Tirthak-bot/Mech-Keeb/PCB/PCB Images/PCB Back.png

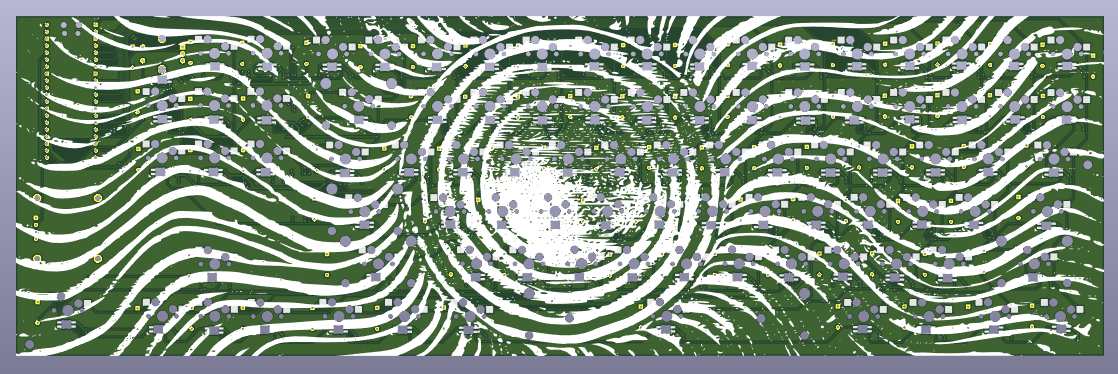
PCB/PCB Images/PCB Back.png
