Tirthak-bot/Mech-Keeb/PCB/PCB Images/PCB Front With Components.png

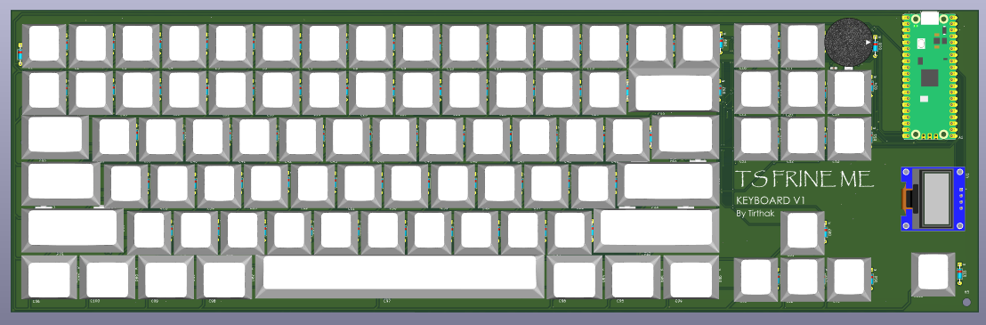
PCB/PCB Images/PCB Front With Components.png
