Tirthak-bot/Mech-Keeb/PCB/Mechanical LP Keyboard.kicad_sch

## KiCad design PCB/Mechanical LP Keyboard.kicad_sch (2026-06-20)

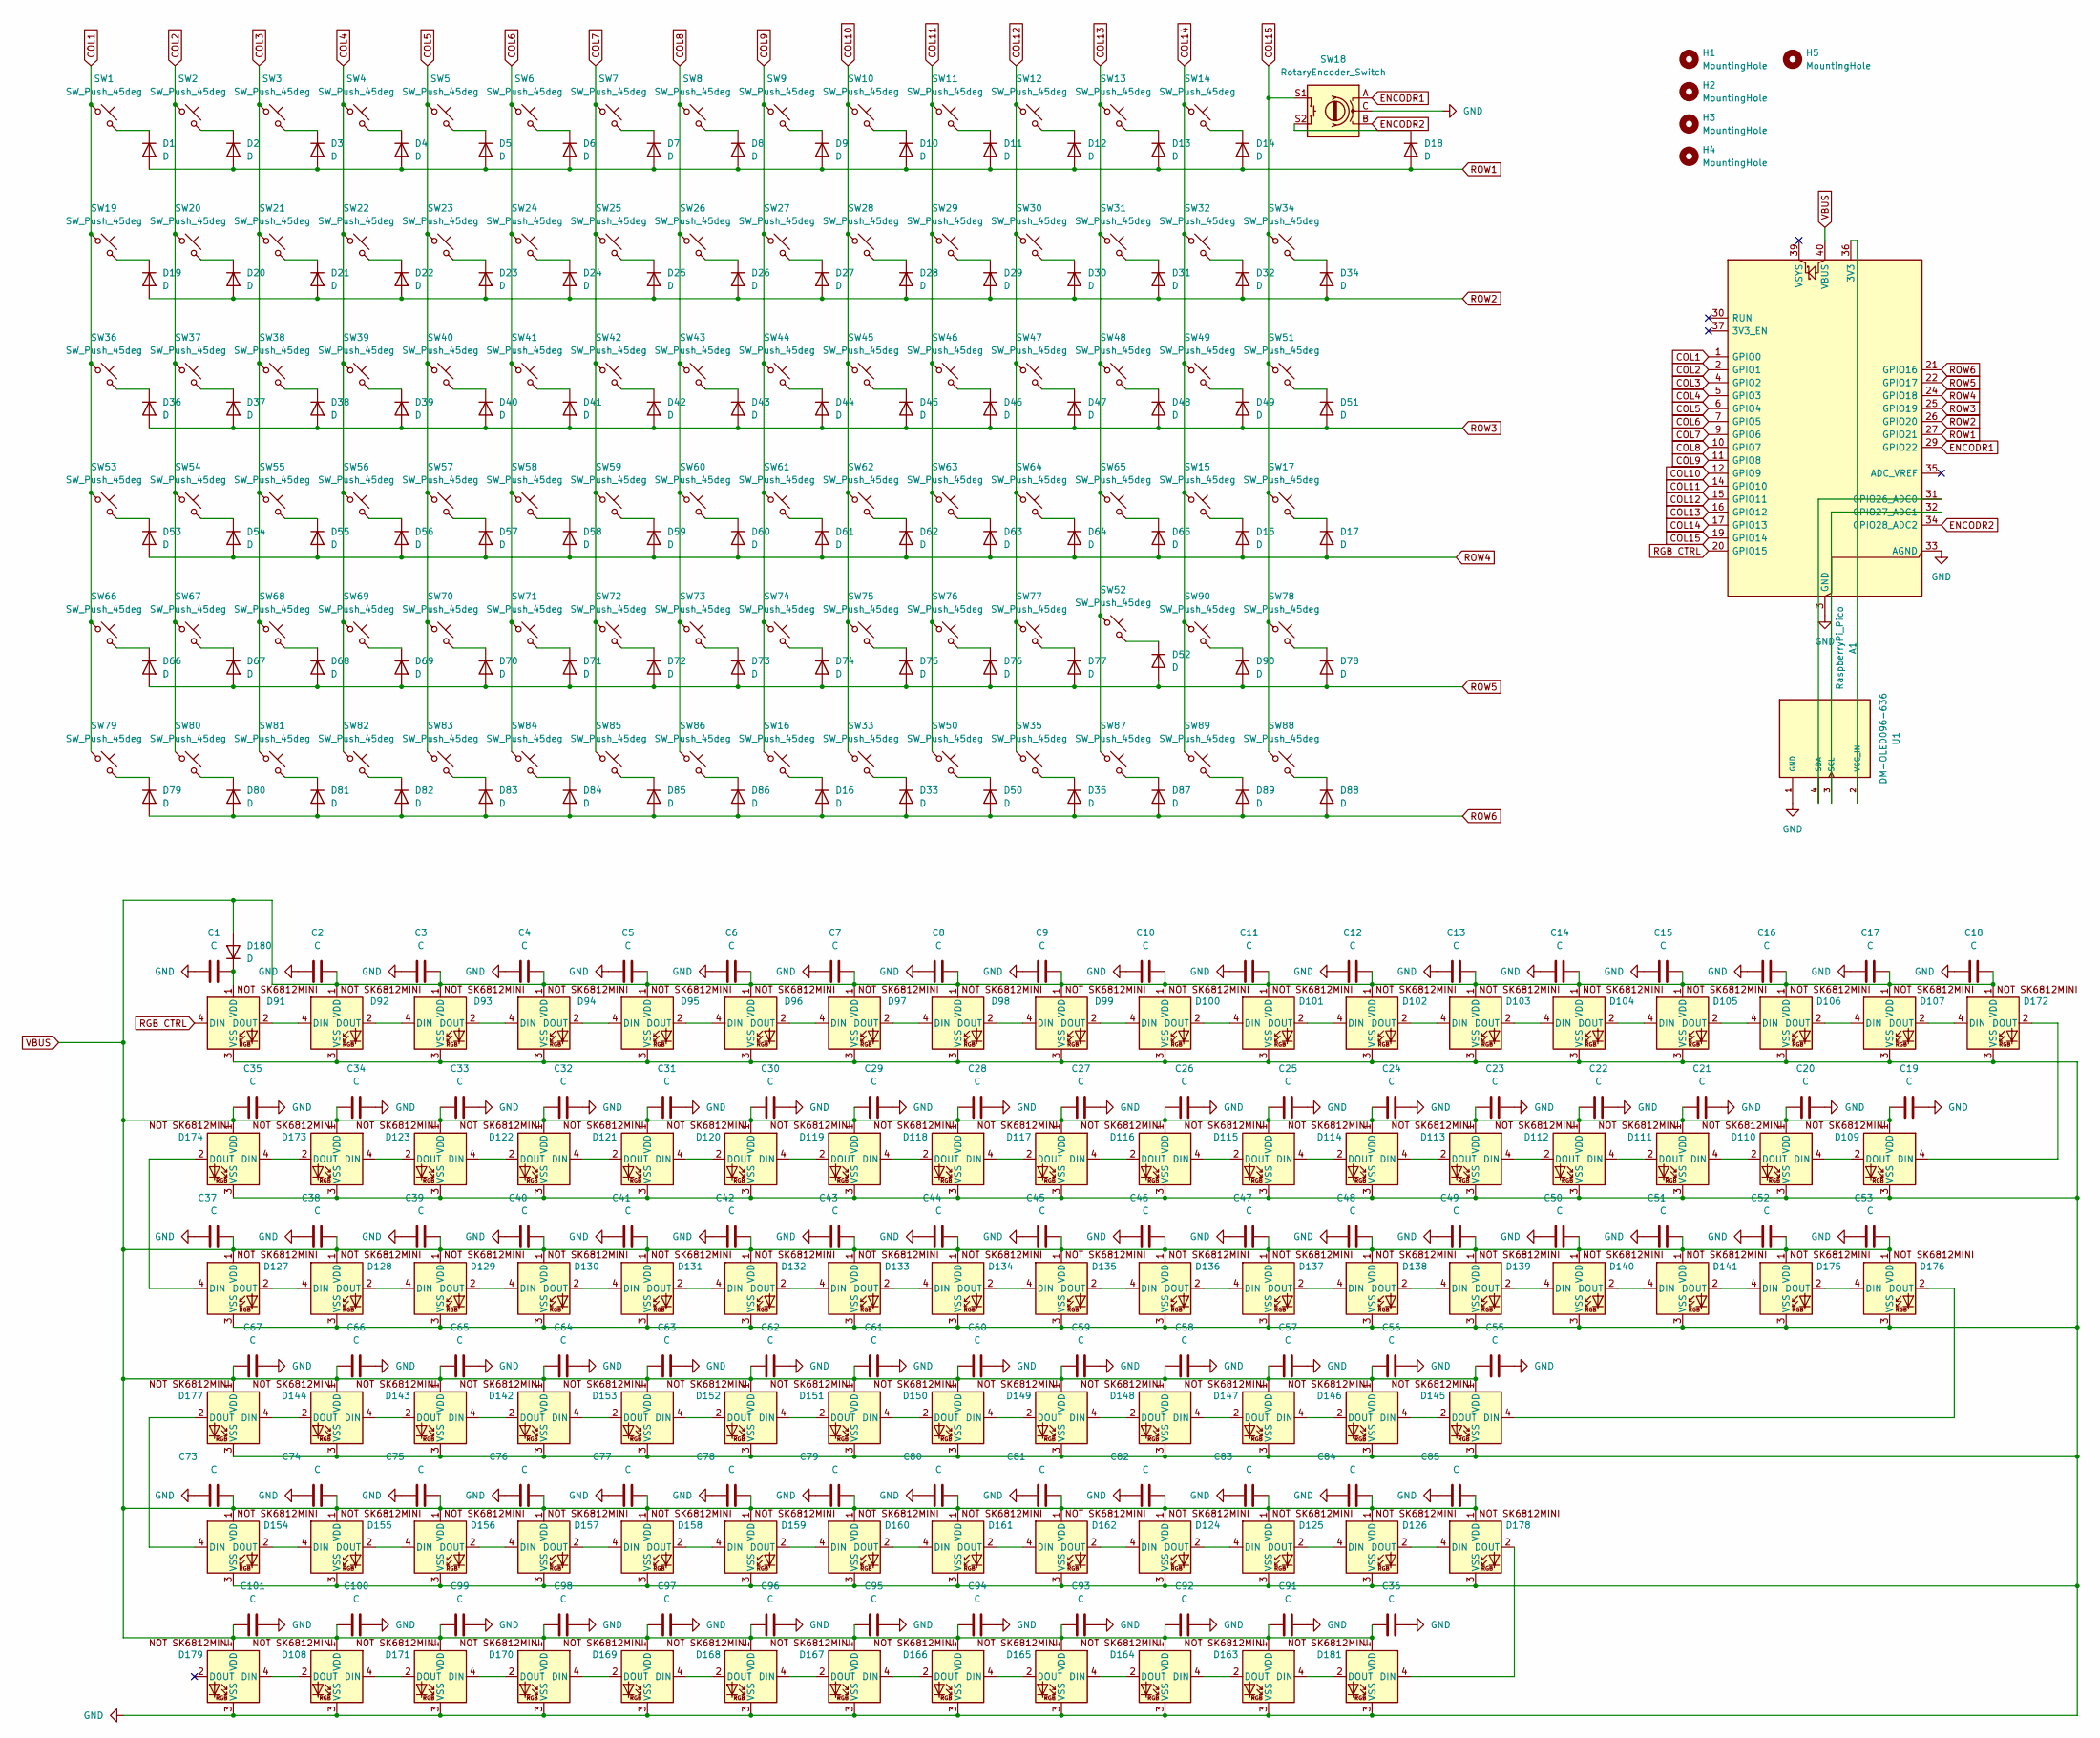
[picture p15: schematic Mechanical LP Keyboard.kicad_sch]

Parts:
A1: RaspberryPi_Pico; RaspberryPi_Pico_Common_Unspecified
C1, C2, C3, C4, C5, C6, C7, C8, C9, C10, C11, C12, C13, C14, C15, C16, C17, C18, C19, C20, C21, C22, C23, C24, C25, C26, C27, C28, C29, C30, C31, C32, C33, C34, C35, C36, C37, C38, C39, C40, C41, C42, C43, C44, C45, C46, C47, C48, C49, C50, C51, C52, C53, C55, C56, C57, C58, C59, C60, C61, C62, C63, C64, C65, C66, C67, C73, C74, C75, C76, C77, C78, C79, C80, C81, C82, C83, C84, C85, C91, C92, C93, C94, C95, C96, C97, C98, C99, C100, C101: C; C_0603_1608Metric_Pad1.08x0.95mm_HandSolder
D1, D2, D3, D4, D5, D6, D7, D8, D9, D10, D11, D12, D13, D14, D15, D16, D17, D18, D19, D20, D21, D22, D23, D24, D25, D26, D27, D28, D29, D30, D31, D32, D33, D34, D35, D36, D37, D38, D39, D40, D41, D42, D43, D44, D45, D46, D47, D48, D49, D50, D51, D52, D53, D54, D55, D56, D57, D58, D59, D60, D61, D62, D63, D64, D65, D66, D67, D68, D69, D70, D71, D72, D73, D74, D75, D76, D77, D78, D79, D80, D81, D82, D83, D84, D85, D86, D87, D88, D89, D90, D180: D; D_DO-35_SOD27_P7.62mm_Horizontal
D91, D92, D93, D94, D95, D96, D97, D98, D99, D100, D101, D102, D103, D104, D105, D106, D107, D108, D109, D110, D111, D112, D113, D114, D115, D116, D117, D118, D119, D120, D121, D122, D123, D124, D125, D126, D127, D128, D129, D130, D131, D132, D133, D134, D135, D136, D137, D138, D139, D140, D141, D142, D143, D144, D145, D146, D147, D148, D149, D150, D151, D152, D153, D154, D155, D156, D157, D158, D159, D160, D161, D162, D163, D164, D165, D166, D167, D168, D169, D170, D171, D172, D173, D174, D175, D176, D177, D178, D179, D181: SK6812MINI-E; SK6812MINI-E_fixed
H1, H2, H3, H4, H5: MountingHole; MountingHole_3.2mm_M3
SW1, SW2, SW3, SW4, SW5, SW6, SW7, SW8, SW9, SW10, SW11, SW12, SW13, SW14, SW15, SW16, SW17, SW19, SW20, SW21, SW22, SW23, SW24, SW25, SW26, SW27, SW28, SW29, SW30, SW31, SW33, SW34, SW35, SW37, SW38, SW39, SW40, SW41, SW42, SW43, SW44, SW45, SW46, SW47, SW48, SW50, SW51, SW52, SW54, SW55, SW56, SW57, SW58, SW59, SW60, SW61, SW62, SW63, SW64, SW67, SW68, SW69, SW70, SW71, SW72, SW73, SW74, SW75, SW76, SW78, SW87, SW88, SW89, SW90: SW_Push_45deg; MX-Hotswap-1U
SW18: RotaryEncoder_Switch; RotaryEncoder_Alps_EC11E-Switch_Vertical_H20mm_CircularMoun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
SW32: SW_Push_45deg; MX-Hotswap-2U-ReversedStabilizers
SW36, SW49: SW_Push_45deg; MX-Hotswap-1.5U
SW53: SW_Push_45deg; MX-Hotswap-1.75U
SW65, SW66: SW_Push_45deg; MX-Hotswap-2.25U-ReversedStabilizers
SW77: SW_Push_45deg; MX-Hotswap-2.75U-ReversedStabilizers
SW79, SW80, SW81, SW82, SW84, SW85, SW86: SW_Push_45deg; MX-Hotswap-1.25U
SW83: SW_Push_45deg; MX-Hotswap-6.25U-ReversedStabilizers
U1: DM-OLED096-636; MODULE_DM-OLED096-636; PARTREV 2018-09-10

Connections:
COL1: A1.1 (GPIO0), SW1.1, SW19.1, SW36.1, SW53.1, SW66.1, SW79.1
COL2: A1.2 (GPIO1), SW2.1, SW20.1, SW37.1, SW54.1, SW67.1, SW80.1
COL3: A1.4 (GPIO2), SW3.1, SW21.1, SW38.1, SW55.1, SW68.1, SW81.1
COL4: A1.5 (GPIO3), SW4.1, SW22.1, SW39.1, SW56.1, SW69.1, SW82.1
COL5: A1.6 (GPIO4), SW5.1, SW23.1, SW40.1, SW57.1, SW70.1, SW83.1
COL6: A1.7 (GPIO5), SW6.1, SW24.1, SW41.1, SW58.1, SW71.1, SW84.1
COL7: A1.9 (GPIO6), SW7.1, SW25.1, SW42.1, SW59.1, SW72.1, SW85.1
COL8: A1.10 (GPIO7), SW8.1, SW26.1, SW43.1, SW60.1, SW73.1, SW86.1
COL9: A1.11 (GPIO8), SW9.1, SW16.1, SW27.1, SW44.1, SW61.1, SW74.1
COL10: A1.12 (GPIO9), SW10.1, SW28.1, SW33.1, SW45.1, SW62.1, SW75.1
COL11: A1.14 (GPIO10), SW11.1, SW29.1, SW46.1, SW50.1, SW63.1, SW76.1
COL12: A1.15 (GPIO11), SW12.1, SW30.1, SW35.1, SW47.1, SW64.1, SW77.1
COL13: A1.16 (GPIO12), SW13.1, SW31.1, SW48.1, SW52.1, SW65.1, SW87.1
COL14: A1.17 (GPIO13), SW14.1, SW15.1, SW32.1, SW49.1, SW89.1, SW90.1
COL15: A1.19 (GPIO14), SW17.1, SW18.S1, SW34.1, SW51.1, SW78.1, SW88.1
ENCODR1: A1.29 (GPIO22), SW18.A
ENCODR2: A1.34 (GPIO28_ADC2), SW18.B
GND: A1.3 (GND), A1.8 (GND), A1.13 (GND), A1.18 (GND), A1.23 (GND), A1.28 (GND), A1.33 (AGND), A1.38 (GND), C1.1, C2.1, C3.1, C4.1, C5.1, C6.1, C7.1, C8.1, C9.1, C10.1, C11.1, C12.1, C13.1, C14.1, C15.1, C16.1, C17.1, C18.1, C19.1, C20.1, C21.1, C22.1, C23.1, C24.1, C25.1, C26.1, C27.1, C28.1, C29.1, C30.1, C31.1, C32.1, C33.1, C34.1, C35.1, C36.1, C37.1, C38.1, C39.1, C40.1, C41.1, C42.1, C43.1, C44.1, C45.1, C46.1, C47.1, C48.1, C49.1, C50.1, C51.1, C52.1, C53.1, C55.1, C56.1, C57.1, C58.1, C59.1, C60.1, C61.1, C62.1, C63.1, C64.1, C65.1, C66.1, C67.1, C73.1, C74.1, C75.1, C76.1, C77.1, C78.1, C79.1, C80.1, C81.1, C82.1, C83.1, C84.1, C85.1, C91.1, C92.1, C93.1, C94.1, C95.1, C96.1, C97.1, C98.1, C99.1, C100.1, C101.1, D91.3 (VSS), D92.3 (VSS), D93.3 (VSS), D94.3 (VSS), D95.3 (VSS), D96.3 (VSS), D97.3 (VSS), D98.3 (VSS), D99.3 (VSS), D100.3 (VSS), D101.3 (VSS), D102.3 (VSS), D103.3 (VSS), D104.3 (VSS), D105.3 (VSS), D106.3 (VSS), D107.3 (VSS), D108.3 (VSS), D109.3 (VSS), D110.3 (VSS), D111.3 (VSS), D112.3 (VSS), D113.3 (VSS), D114.3 (VSS), D115.3 (VSS), D116.3 (VSS), D117.3 (VSS), D118.3 (VSS), D119.3 (VSS), D120.3 (VSS), D121.3 (VSS), D122.3 (VSS), D123.3 (VSS), D124.3 (VSS), D125.3 (VSS), D126.3 (VSS), D127.3 (VSS), D128.3 (VSS), D129.3 (VSS), D130.3 (VSS), D131.3 (VSS), D132.3 (VSS), D133.3 (VSS), D134.3 (VSS), D135.3 (VSS), D136.3 (VSS), D137.3 (VSS), D138.3 (VSS), D139.3 (VSS), D140.3 (VSS), D141.3 (VSS), D142.3 (VSS), D143.3 (VSS), D144.3 (VSS), D145.3 (VSS), D146.3 (VSS), D147.3 (VSS), D148.3 (VSS), D149.3 (VSS), D150.3 (VSS), D151.3 (VSS), D152.3 (VSS), D153.3 (VSS), D154.3 (VSS), D155.3 (VSS), D156.3 (VSS), D157.3 (VSS), D158.3 (VSS), D159.3 (VSS), D160.3 (VSS), D161.3 (VSS), D162.3 (VSS), D163.3 (VSS), D164.3 (VSS), D165.3 (VSS), D166.3 (VSS), D167.3 (VSS), D168.3 (VSS), D169.3 (VSS), D170.3 (VSS), D171.3 (VSS), D172.3 (VSS), D173.3 (VSS), D174.3 (VSS), D175.3 (VSS), D176.3 (VSS), D177.3 (VSS), D178.3 (VSS), D179.3 (VSS), D181.3 (VSS), SW18.C, U1.1 (GND)
unnamed: A1.31 (GPIO26_ADC0), U1.4 (SDA)
unnamed: A1.32 (GPIO27_ADC1), U1.3 (SCL)
unnamed: A1.36 (3V3), U1.2 (VCC_IN)
unnamed: C1.2, D91.1 (VDD), D180.1 (K)
unnamed: D1.1 (K), SW1.2
unnamed: D2.1 (K), SW2.2
unnamed: D3.1 (K), SW3.2
unnamed: D4.1 (K), SW4.2
unnamed: D5.1 (K), SW5.2
unnamed: D6.1 (K), SW6.2
unnamed: D7.1 (K), SW7.2
unnamed: D8.1 (K), SW8.2
unnamed: D9.1 (K), SW9.2
unnamed: D10.1 (K), SW10.2
unnamed: D11.1 (K), SW11.2
unnamed: D12.1 (K), SW12.2
unnamed: D13.1 (K), SW13.2
unnamed: D14.1 (K), SW14.2
unnamed: D15.1 (K), SW15.2
unnamed: D16.1 (K), SW16.2
unnamed: D17.1 (K), SW17.2
unnamed: D18.1 (K), SW18.S2
unnamed: D19.1 (K), SW19.2
unnamed: D20.1 (K), SW20.2
unnamed: D21.1 (K), SW21.2
unnamed: D22.1 (K), SW22.2
unnamed: D23.1 (K), SW23.2
unnamed: D24.1 (K), SW24.2
unnamed: D25.1 (K), SW25.2
unnamed: D26.1 (K), SW26.2
unnamed: D27.1 (K), SW27.2
unnamed: D28.1 (K), SW28.2
unnamed: D29.1 (K), SW29.2
unnamed: D30.1 (K), SW30.2
unnamed: D31.1 (K), SW31.2
unnamed: D32.1 (K), SW32.2
unnamed: D33.1 (K), SW33.2
unnamed: D34.1 (K), SW34.2
unnamed: D35.1 (K), SW35.2
unnamed: D36.1 (K), SW36.2
unnamed: D37.1 (K), SW37.2
unnamed: D38.1 (K), SW38.2
unnamed: D39.1 (K), SW39.2
unnamed: D40.1 (K), SW40.2
unnamed: D41.1 (K), SW41.2
unnamed: D42.1 (K), SW42.2
unnamed: D43.1 (K), SW43.2
unnamed: D44.1 (K), SW44.2
unnamed: D45.1 (K), SW45.2
unnamed: D46.1 (K), SW46.2
unnamed: D47.1 (K), SW47.2
unnamed: D48.1 (K), SW48.2
unnamed: D49.1 (K), SW49.2
unnamed: D50.1 (K), SW50.2
unnamed: D51.1 (K), SW51.2
unnamed: D52.1 (K), SW52.2
unnamed: D53.1 (K), SW53.2
unnamed: D54.1 (K), SW54.2
unnamed: D55.1 (K), SW55.2
unnamed: D56.1 (K), SW56.2
unnamed: D57.1 (K), SW57.2
unnamed: D58.1 (K), SW58.2
unnamed: D59.1 (K), SW59.2
unnamed: D60.1 (K), SW60.2
unnamed: D61.1 (K), SW61.2
unnamed: D62.1 (K), SW62.2
unnamed: D63.1 (K), SW63.2
unnamed: D64.1 (K), SW64.2
unnamed: D65.1 (K), SW65.2
unnamed: D66.1 (K), SW66.2
unnamed: D67.1 (K), SW67.2
unnamed: D68.1 (K), SW68.2
unnamed: D69.1 (K), SW69.2
unnamed: D70.1 (K), SW70.2
unnamed: D71.1 (K), SW71.2
unnamed: D72.1 (K), SW72.2
unnamed: D73.1 (K), SW73.2
unnamed: D74.1 (K), SW74.2
unnamed: D75.1 (K), SW75.2
unnamed: D76.1 (K), SW76.2
unnamed: D77.1 (K), SW77.2
unnamed: D78.1 (K), SW78.2
unnamed: D79.1 (K), SW79.2
unnamed: D80.1 (K), SW80.2
unnamed: D81.1 (K), SW81.2
unnamed: D82.1 (K), SW82.2
unnamed: D83.1 (K), SW83.2
unnamed: D84.1 (K), SW84.2
unnamed: D85.1 (K), SW85.2
unnamed: D86.1 (K), SW86.2
unnamed: D87.1 (K), SW87.2
unnamed: D88.1 (K), SW88.2
unnamed: D89.1 (K), SW89.2
unnamed: D90.1 (K), SW90.2
unnamed: D91.2 (DOUT), D92.4 (DIN)
unnamed: D92.2 (DOUT), D93.4 (DIN)
unnamed: D93.2 (DOUT), D94.4 (DIN)
unnamed: D94.2 (DOUT), D95.4 (DIN)
unnamed: D95.2 (DOUT), D96.4 (DIN)
unnamed: D96.2 (DOUT), D97.4 (DIN)
unnamed: D97.2 (DOUT), D98.4 (DIN)
unnamed: D98.2 (DOUT), D99.4 (DIN)
unnamed: D100.2 (DOUT), D101.4 (DIN)
unnamed: D99.2 (DOUT), D100.4 (DIN)
unnamed: D101.2 (DOUT), D102.4 (DIN)
unnamed: D102.2 (DOUT), D103.4 (DIN)
unnamed: D103.2 (DOUT), D104.4 (DIN)
unnamed: D104.2 (DOUT), D105.4 (DIN)
unnamed: D105.2 (DOUT), D106.4 (DIN)
unnamed: D106.2 (DOUT), D107.4 (DIN)
unnamed: D107.2 (DOUT), D172.4 (DIN)
unnamed: D108.2 (DOUT), D179.4 (DIN)
unnamed: D108.4 (DIN), D171.2 (DOUT)
unnamed: D109.2 (DOUT), D110.4 (DIN)
unnamed: D109.4 (DIN), D172.2 (DOUT)
unnamed: D110.2 (DOUT), D111.4 (DIN)
unnamed: D111.2 (DOUT), D112.4 (DIN)
unnamed: D112.2 (DOUT), D113.4 (DIN)
unnamed: D113.2 (DOUT), D114.4 (DIN)
unnamed: D114.2 (DOUT), D115.4 (DIN)
unnamed: D115.2 (DOUT), D116.4 (DIN)
unnamed: D116.2 (DOUT), D117.4 (DIN)
unnamed: D117.2 (DOUT), D118.4 (DIN)
unnamed: D118.2 (DOUT), D119.4 (DIN)
unnamed: D119.2 (DOUT), D120.4 (DIN)
unnamed: D120.2 (DOUT), D121.4 (DIN)
unnamed: D121.2 (DOUT), D122.4 (DIN)
unnamed: D122.2 (DOUT), D123.4 (DIN)
unnamed: D123.2 (DOUT), D173.4 (DIN)
unnamed: D124.2 (DOUT), D125.4 (DIN)
unnamed: D124.4 (DIN), D162.2 (DOUT)
unnamed: D125.2 (DOUT), D126.4 (DIN)
unnamed: D126.2 (DOUT), D178.4 (DIN)
unnamed: D127.2 (DOUT), D128.4 (DIN)
unnamed: D127.4 (DIN), D174.2 (DOUT)
unnamed: D128.2 (DOUT), D129.4 (DIN)
unnamed: D129.2 (DOUT), D130.4 (DIN)
unnamed: D130.2 (DOUT), D131.4 (DIN)
unnamed: D131.2 (DOUT), D132.4 (DIN)
unnamed: D132.2 (DOUT), D133.4 (DIN)
unnamed: D133.2 (DOUT), D134.4 (DIN)
unnamed: D134.2 (DOUT), D135.4 (DIN)
unnamed: D135.2 (DOUT), D136.4 (DIN)
unnamed: D136.2 (DOUT), D137.4 (DIN)
unnamed: D137.2 (DOUT), D138.4 (DIN)
unnamed: D138.2 (DOUT), D139.4 (DIN)
unnamed: D139.2 (DOUT), D140.4 (DIN)
unnamed: D140.2 (DOUT), D141.4 (DIN)
unnamed: D141.2 (DOUT), D175.4 (DIN)
unnamed: D142.2 (DOUT), D143.4 (DIN)
unnamed: D142.4 (DIN), D153.2 (DOUT)
unnamed: D143.2 (DOUT), D144.4 (DIN)
unnamed: D144.2 (DOUT), D177.4 (DIN)
unnamed: D145.2 (DOUT), D146.4 (DIN)
unnamed: D145.4 (DIN), D176.2 (DOUT)
unnamed: D146.2 (DOUT), D147.4 (DIN)
unnamed: D147.2 (DOUT), D148.4 (DIN)
unnamed: D148.2 (DOUT), D149.4 (DIN)
unnamed: D149.2 (DOUT), D150.4 (DIN)
unnamed: D150.2 (DOUT), D151.4 (DIN)
unnamed: D151.2 (DOUT), D152.4 (DIN)
unnamed: D152.2 (DOUT), D153.4 (DIN)
unnamed: D154.2 (DOUT), D155.4 (DIN)
unnamed: D154.4 (DIN), D177.2 (DOUT)
unnamed: D155.2 (DOUT), D156.4 (DIN)
unnamed: D156.2 (DOUT), D157.4 (DIN)
unnamed: D157.2 (DOUT), D158.4 (DIN)
unnamed: D158.2 (DOUT), D159.4 (DIN)
unnamed: D159.2 (DOUT), D160.4 (DIN)
unnamed: D160.2 (DOUT), D161.4 (DIN)
unnamed: D161.2 (DOUT), D162.4 (DIN)
unnamed: D163.2 (DOUT), D164.4 (DIN)
unnamed: D163.4 (DIN), D181.2 (DOUT)
unnamed: D164.2 (DOUT), D165.4 (DIN)
unnamed: D165.2 (DOUT), D166.4 (DIN)
unnamed: D166.2 (DOUT), D167.4 (DIN)
unnamed: D167.2 (DOUT), D168.4 (DIN)
unnamed: D168.2 (DOUT), D169.4 (DIN)
unnamed: D169.2 (DOUT), D170.4 (DIN)
unnamed: D170.2 (DOUT), D171.4 (DIN)
unnamed: D173.2 (DOUT), D174.4 (DIN)
unnamed: D175.2 (DOUT), D176.4 (DIN)
unnamed: D178.2 (DOUT), D181.4 (DIN)
RGB CTRL: A1.20 (GPIO15), D91.4 (DIN)
ROW1: A1.27 (GPIO21), D1.2 (A), D2.2 (A), D3.2 (A), D4.2 (A), D5.2 (A), D6.2 (A), D7.2 (A), D8.2 (A), D9.2 (A), D10.2 (A), D11.2 (A), D12.2 (A), D13.2 (A), D14.2 (A), D18.2 (A)
ROW2: A1.26 (GPIO20), D19.2 (A), D20.2 (A), D21.2 (A), D22.2 (A), D23.2 (A), D24.2 (A), D25.2 (A), D26.2 (A), D27.2 (A), D28.2 (A), D29.2 (A), D30.2 (A), D31.2 (A), D32.2 (A), D34.2 (A)
ROW3: A1.25 (GPIO19), D36.2 (A), D37.2 (A), D38.2 (A), D39.2 (A), D40.2 (A), D41.2 (A), D42.2 (A), D43.2 (A), D44.2 (A), D45.2 (A), D46.2 (A), D47.2 (A), D48.2 (A), D49.2 (A), D51.2 (A)
ROW4: A1.24 (GPIO18), D15.2 (A), D17.2 (A), D53.2 (A), D54.2 (A), D55.2 (A), D56.2 (A), D57.2 (A), D58.2 (A), D59.2 (A), D60.2 (A), D61.2 (A), D62.2 (A), D63.2 (A), D64.2 (A), D65.2 (A)
ROW5: A1.22 (GPIO17), D52.2 (A), D66.2 (A), D67.2 (A), D68.2 (A), D69.2 (A), D70.2 (A), D71.2 (A), D72.2 (A), D73.2 (A), D74.2 (A), D75.2 (A), D76.2 (A), D77.2 (A), D78.2 (A), D90.2 (A)
ROW6: A1.21 (GPIO16), D16.2 (A), D33.2 (A), D35.2 (A), D50.2 (A), D79.2 (A), D80.2 (A), D81.2 (A), D82.2 (A), D83.2 (A), D84.2 (A), D85.2 (A), D86.2 (A), D87.2 (A), D88.2 (A), D89.2 (A)
VBUS: A1.40 (VBUS), C2.2, C3.2, C4.2, C5.2, C6.2, C7.2, C8.2, C9.2, C10.2, C11.2, C12.2, C13.2, C14.2, C15.2, C16.2, C17.2, C18.2, C19.2, C20.2, C21.2, C22.2, C23.2, C24.2, C25.2, C26.2, C27.2, C28.2, C29.2, C30.2, C31.2, C32.2, C33.2, C34.2, C35.2, C36.2, C37.2, C38.2, C39.2, C40.2, C41.2, C42.2, C43.2, C44.2, C45.2, C46.2, C47.2, C48.2, C49.2, C50.2, C51.2, C52.2, C53.2, C55.2, C56.2, C57.2, C58.2, C59.2, C60.2, C61.2, C62.2, C63.2, C64.2, C65.2, C66.2, C67.2, C73.2, C74.2, C75.2, C76.2, C77.2, C78.2, C79.2, C80.2, C81.2, C82.2, C83.2, C84.2, C85.2, C91.2, C92.2, C93.2, C94.2, C95.2, C96.2, C97.2, C98.2, C99.2, C100.2, C101.2, D92.1 (VDD), D93.1 (VDD), D94.1 (VDD), D95.1 (VDD), D96.1 (VDD), D97.1 (VDD), D98.1 (VDD), D99.1 (VDD), D100.1 (VDD), D101.1 (VDD), D102.1 (VDD), D103.1 (VDD), D104.1 (VDD), D105.1 (VDD), D106.1 (VDD), D107.1 (VDD), D108.1 (VDD), D109.1 (VDD), D110.1 (VDD), D111.1 (VDD), D112.1 (VDD), D113.1 (VDD), D114.1 (VDD), D115.1 (VDD), D116.1 (VDD), D117.1 (VDD), D118.1 (VDD), D119.1 (VDD), D120.1 (VDD), D121.1 (VDD), D122.1 (VDD), D123.1 (VDD), D124.1 (VDD), D125.1 (VDD), D126.1 (VDD), D127.1 (VDD), D128.1 (VDD), D129.1 (VDD), D130.1 (VDD), D131.1 (VDD), D132.1 (VDD), D133.1 (VDD), D134.1 (VDD), D135.1 (VDD), D136.1 (VDD), D137.1 (VDD), D138.1 (VDD), D139.1 (VDD), D140.1 (VDD), D141.1 (VDD), D142.1 (VDD), D143.1 (VDD), D144.1 (VDD), D145.1 (VDD), D146.1 (VDD), D147.1 (VDD), D148.1 (VDD), D149.1 (VDD), D150.1 (VDD), D151.1 (VDD), D152.1 (VDD), D153.1 (VDD), D154.1 (VDD), D155.1 (VDD), D156.1 (VDD), D157.1 (VDD), D158.1 (VDD), D159.1 (VDD), D160.1 (VDD), D161.1 (VDD), D162.1 (VDD), D163.1 (VDD), D164.1 (VDD), D165.1 (VDD), D166.1 (VDD), D167.1 (VDD), D168.1 (VDD), D169.1 (VDD), D170.1 (VDD), D171.1 (VDD), D172.1 (VDD), D173.1 (VDD), D174.1 (VDD), D175.1 (VDD), D176.1 (VDD), D177.1 (VDD), D178.1 (VDD), D179.1 (VDD), D180.2 (A), D181.1 (VDD)
